LDZPLN1/RP2040-GPS/RP2040 GPS.kicad_sch

## KiCad design RP2040 GPS.kicad_sch (2022-03-28)

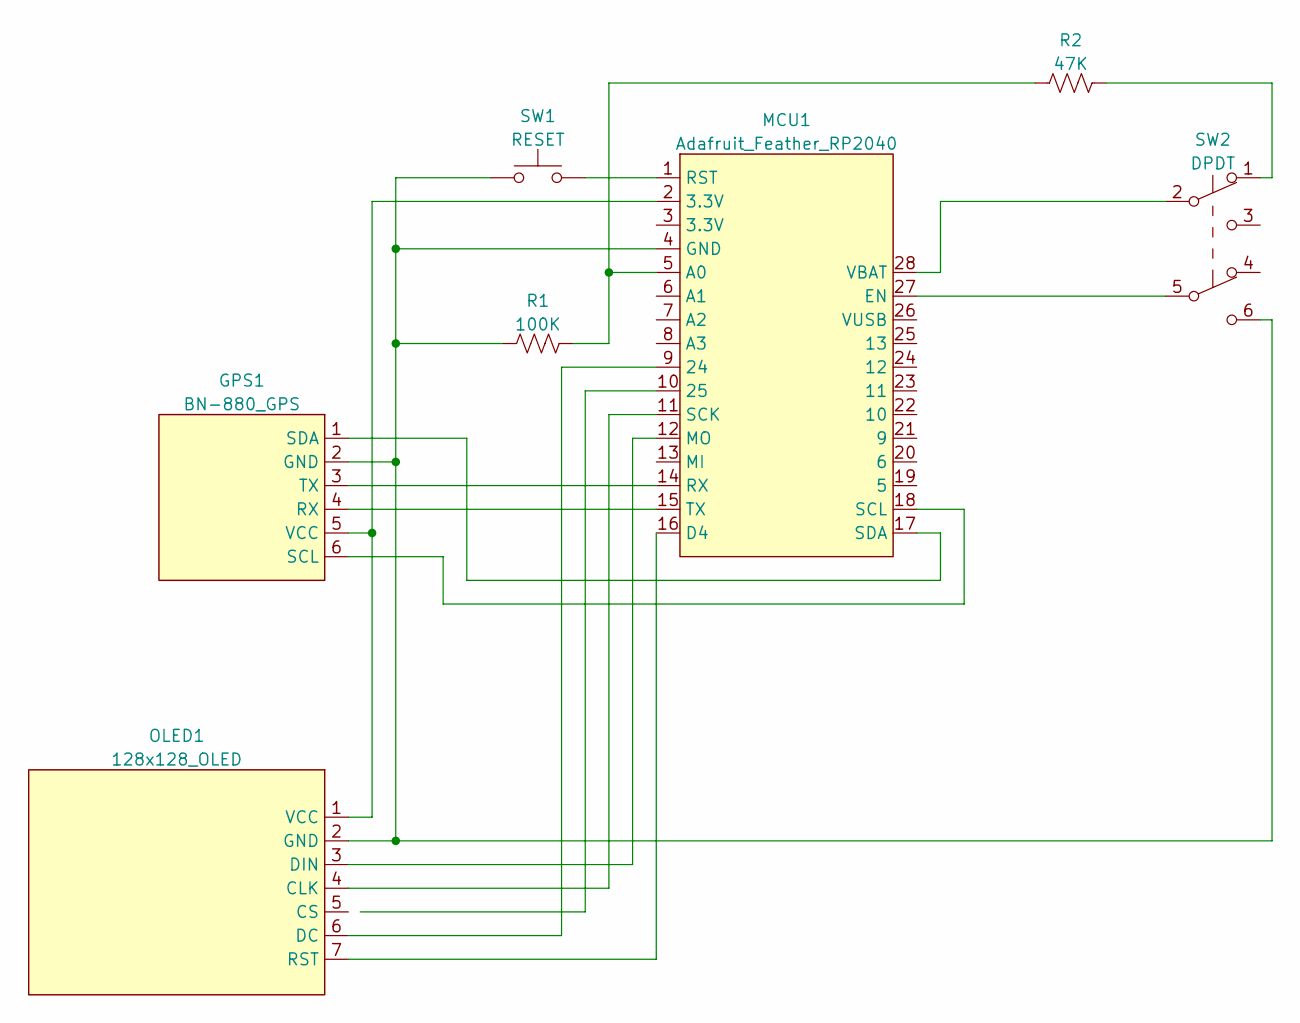
[picture p2: schematic RP2040 GPS.kicad_sch]

Parts:
GPS1: BN-880_GPS
MCU1: Adafruit_Feather_RP2040
OLED1: 128x128_OLED
R1: 100K
R2: 47K
SW1: RESET
SW2: DPDT

Connections:
unnamed: GPS1.1 (SDA), MCU1.17 (SDA)
unnamed: GPS1.2 (GND), MCU1.4 (GND), OLED1.2 (GND), R1.1, SW1.1, SW2.6 (C)
unnamed: GPS1.3 (TX), MCU1.14 (RX)
unnamed: GPS1.4 (RX), MCU1.15 (TX)
unnamed: GPS1.5 (VCC), MCU1.2 (3.3V), OLED1.1 (VCC)
unnamed: GPS1.6 (SCL), MCU1.18 (SCL)
unnamed: MCU1.1 (RST), SW1.2
unnamed: MCU1.5 (A0), R1.2, R2.1
unnamed: MCU1.9 (24), OLED1.6 (DC)
unnamed: MCU1.11 (SCK), OLED1.4 (CLK)
unnamed: MCU1.12 (MO), OLED1.3 (DIN)
unnamed: MCU1.16 (D4), OLED1.7 (RST)
unnamed: MCU1.27 (EN), SW2.5 (B)
unnamed: MCU1.28 (VBAT), SW2.2 (B)
unnamed: R2.2, SW2.1 (A)
